jonte1346/Service-Robotics/CAD/Laser files/Front Panel 2.DXF

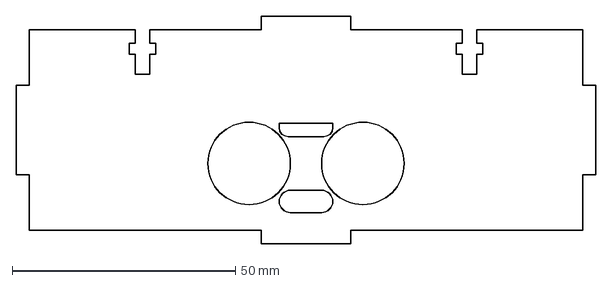
[picture p29: CAD file, 2024-11-29]
CAD/Laser files/Front Panel 2.DXF
130.0 x 51.0 mm
