jonte1346/Service-Robotics/CAD/Batterihållare/Bas.SLDPRT

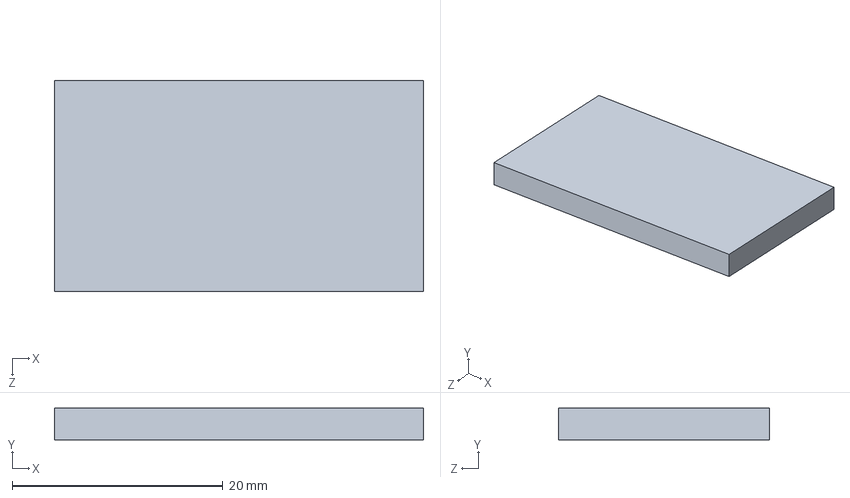
[picture p30: CAD file, 2024-12-06]
CAD/Batterihållare/Bas.SLDPRT
35.0 x 3.00 x 20.0 mm
