jonte1346/Service-Robotics/CAD/Body V5 (V2)/Side Panel 2.SLDPRT

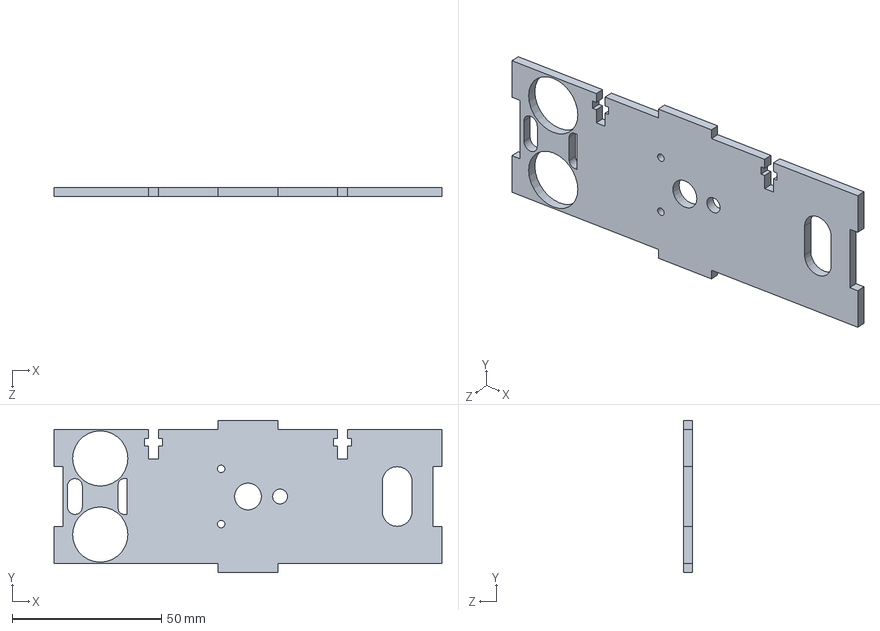
[picture p31: CAD file, 2024-11-29]
CAD/Body V5 (V2)/Side Panel 2.SLDPRT
130.0 x 51.0 x 3.00 mm
