jonte1346/Service-Robotics/CAD/Laser files/Cage Side.DXF

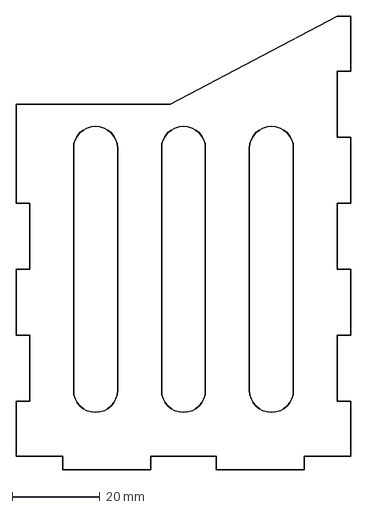
[picture p32: CAD file, 2024-11-29]
CAD/Laser files/Cage Side.DXF
76.0 x 103.0 mm
