jonte1346/Service-Robotics/CAD/Batterihållare/Front.SLDPRT

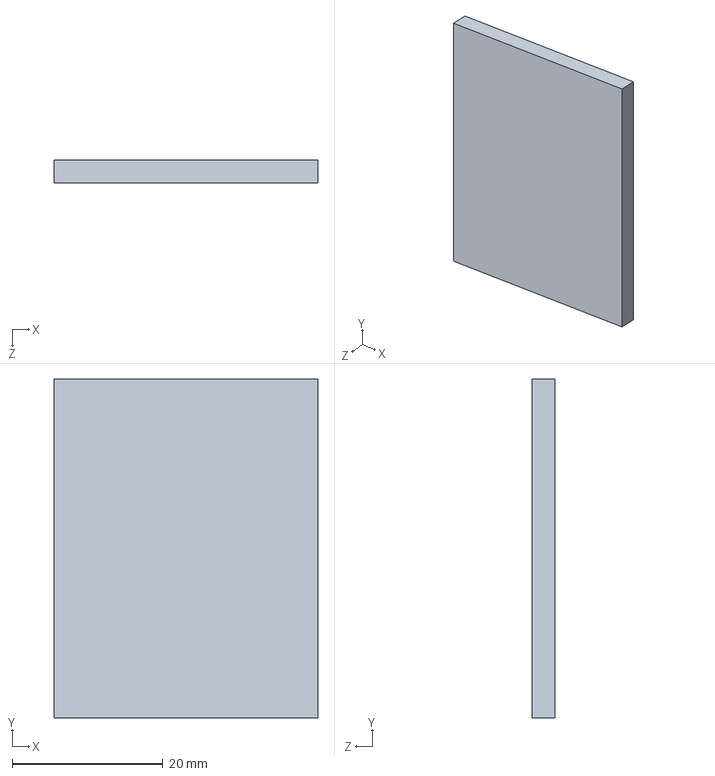
[picture p33: CAD file, 2024-12-06]
CAD/Batterihållare/Front.SLDPRT
35.0 x 45.0 x 3.00 mm
