jonte1346/Service-Robotics/CAD/Laser files/Side Panel 2.DXF

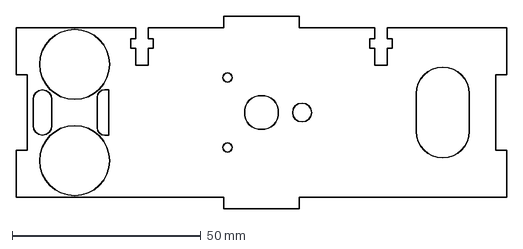
[picture p34: CAD file, 2024-11-29]
CAD/Laser files/Side Panel 2.DXF
130.0 x 51.0 mm
