jonte1346/Service-Robotics/CAD/Body V5 (V2)/Cage Side.SLDPRT

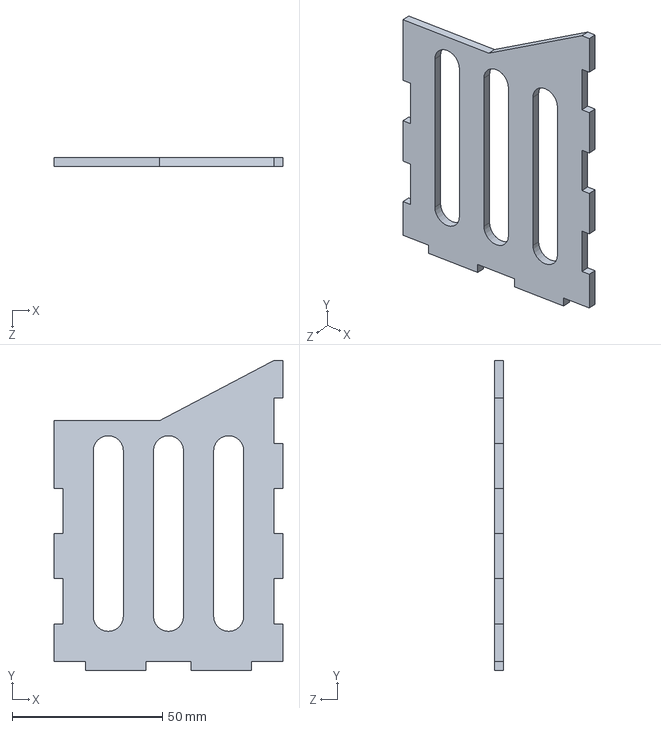
[picture p35: CAD file, 2024-11-29]
CAD/Body V5 (V2)/Cage Side.SLDPRT
76.0 x 103.0 x 3.00 mm
