jonte1346/Service-Robotics/CAD/Laser files/Cage Right.DXF

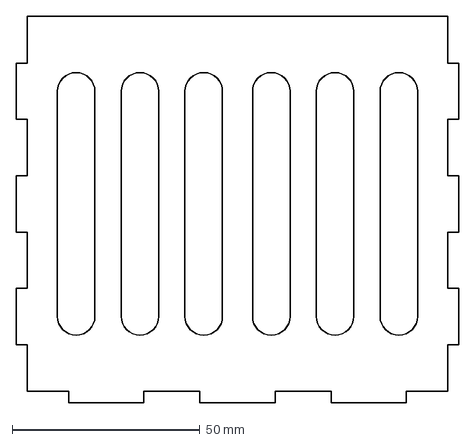
[picture p36: CAD file, 2024-11-29]
CAD/Laser files/Cage Right.DXF
118.0 x 103.0 mm
