jonte1346/Service-Robotics/CAD/Body V5 (V2)/Arm.SLDPRT

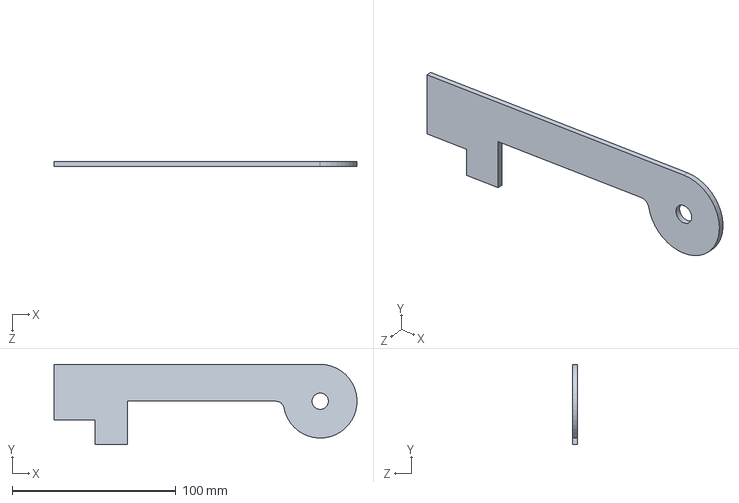
[picture p37: CAD file, 2024-11-29]
CAD/Body V5 (V2)/Arm.SLDPRT
185.0 x 49.0 x 3.00 mm
