jonte1346/Service-Robotics/CAD/Laser files/Top Panel 2.DXF

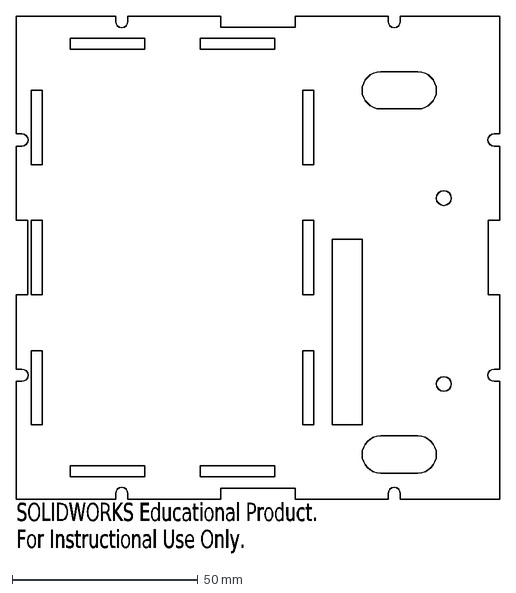
[picture p38: CAD file, 2024-11-29]
CAD/Laser files/Top Panel 2.DXF
SOLIDWORKS Educational Product.
For Instructional Use Only.
