jonte1346/Service-Robotics/CAD/Laser files/Arm - arm spacer.DXF

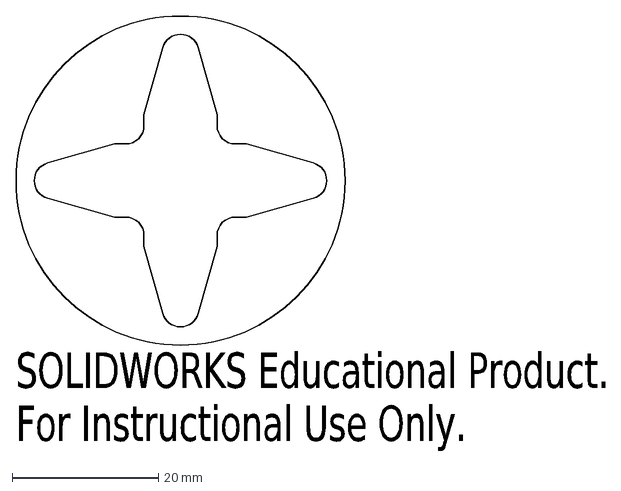
[picture p40: CAD file, 2024-11-29]
CAD/Laser files/Arm - arm spacer.DXF
SOLIDWORKS Educational Product.
For Instructional Use Only.
