jonte1346/Service-Robotics/CAD/Body V5 (V2)/Cage Left.SLDPRT

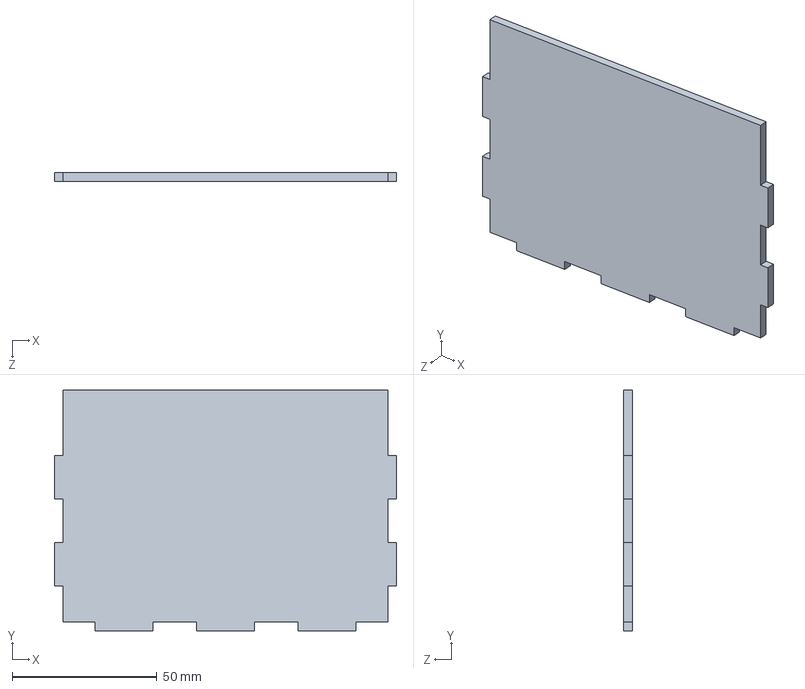
[picture p41: CAD file, 2024-11-29]
CAD/Body V5 (V2)/Cage Left.SLDPRT
118.0 x 83.0 x 3.00 mm
