jonte1346/Service-Robotics/CAD/Laser files/Cage Left.DXF

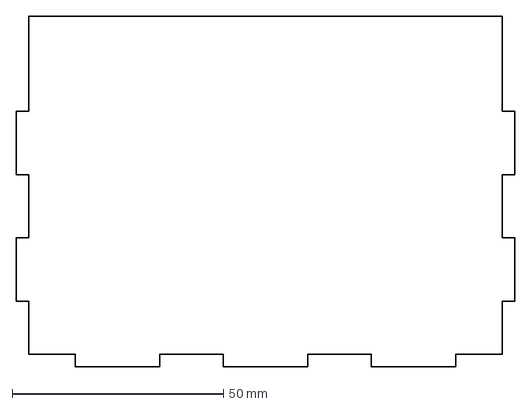
[picture p42: CAD file, 2024-11-29]
CAD/Laser files/Cage Left.DXF
118.0 x 83.0 mm
