jonte1346/Service-Robotics/CAD/Laser files/Arm - gripper support.DXF

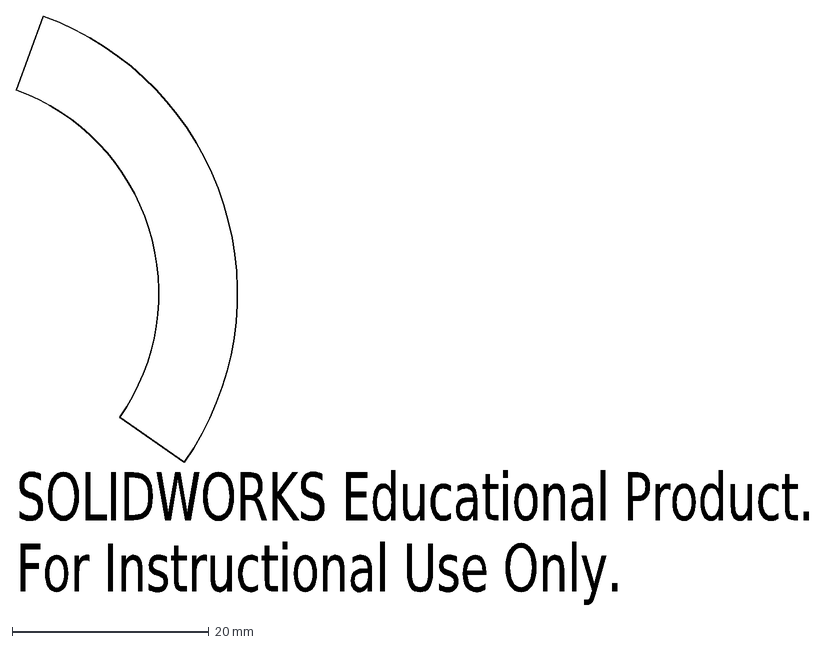
[picture p43: CAD file, 2024-11-29]
CAD/Laser files/Arm - gripper support.DXF
SOLIDWORKS Educational Product.
For Instructional Use Only.
