jonte1346/Service-Robotics/CAD/Body V5 (V2)/Top Panel 2.SLDPRT

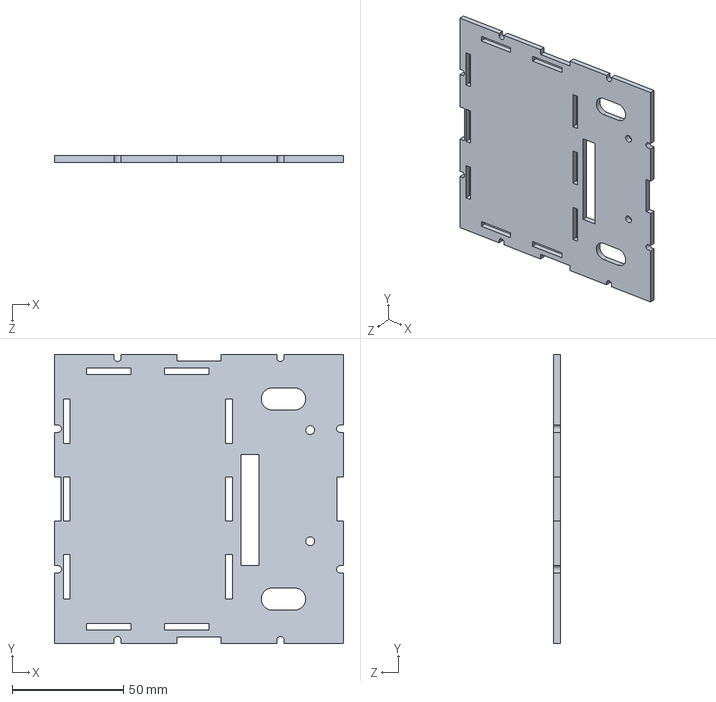
[picture p44: CAD file, 2024-11-28]
CAD/Body V5 (V2)/Top Panel 2.SLDPRT
130.0 x 130.0 x 3.00 mm
