jonte1346/Service-Robotics/CAD/Laser files/Arm - hålbricka.DXF

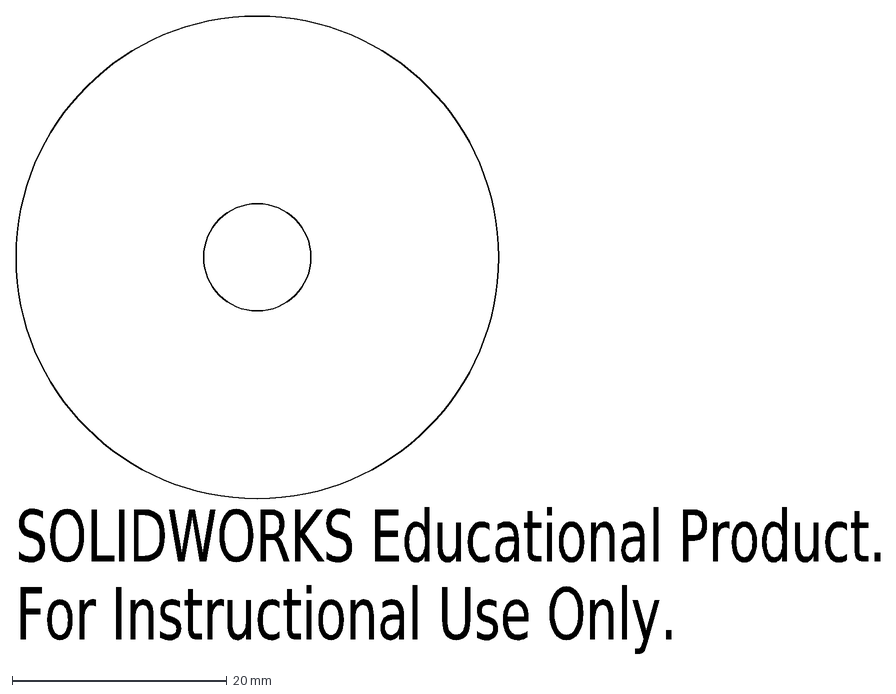
[picture p45: CAD file, 2024-11-29]
CAD/Laser files/Arm - hålbricka.DXF
SOLIDWORKS Educational Product.
For Instructional Use Only.
