jonte1346/Service-Robotics/CAD/Body V5 (V2)/Spacer.SLDPRT

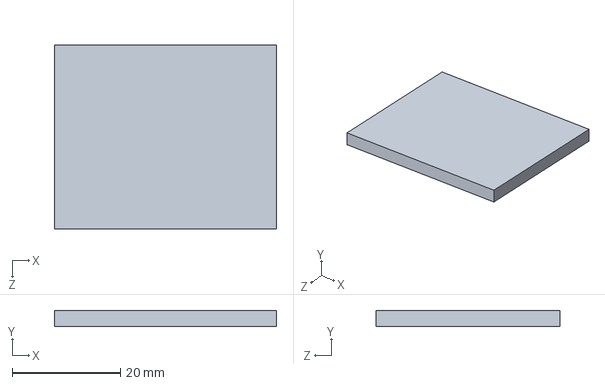
[picture p46: CAD file, 2024-11-27]
CAD/Body V5 (V2)/Spacer.SLDPRT
41.0 x 3.00 x 34.0 mm
