jonte1346/Service-Robotics/CAD/Laser files/Arm.DXF

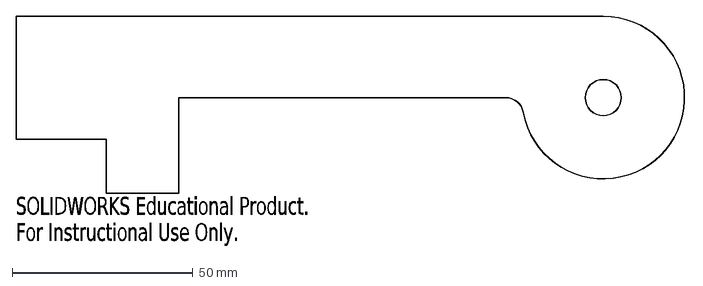
[picture p47: CAD file, 2024-11-29]
CAD/Laser files/Arm.DXF
SOLIDWORKS Educational Product.
For Instructional Use Only.
