jonte1346/Service-Robotics/CAD/Body V5 (V2)/Servo bult platta.SLDPRT

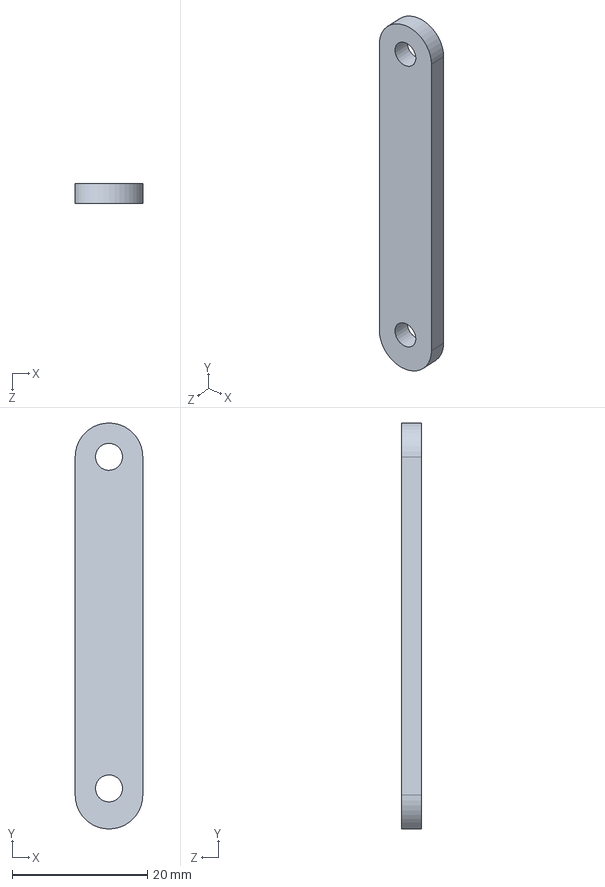
[picture p48: CAD file, 2024-11-25]
CAD/Body V5 (V2)/Servo bult platta.SLDPRT
10.0 x 60.0 x 3.00 mm
