jonte1346/Service-Robotics/CAD/Laser files/Servo Spacer.DXF

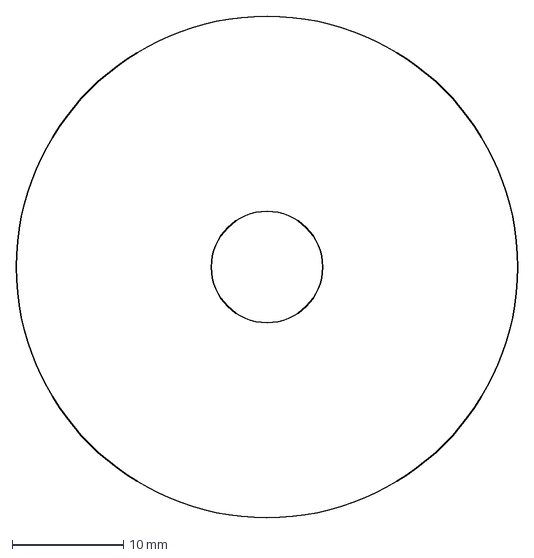
[picture p49: CAD file, 2024-11-20]
CAD/Laser files/Servo Spacer.DXF
45.0 x 45.0 mm
