jonte1346/Service-Robotics/CAD/Laser files/Servo bult platta.DXF

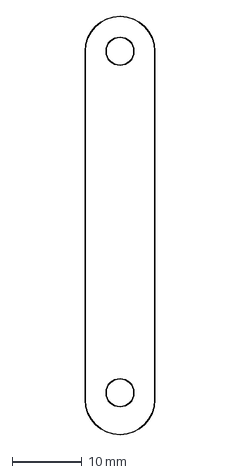
[picture p50: CAD file, 2024-11-20]
CAD/Laser files/Servo bult platta.DXF
10.0 x 60.0 mm
