jonte1346/Service-Robotics/CAD/Body V5 (V2)/Cage ramp.SLDPRT

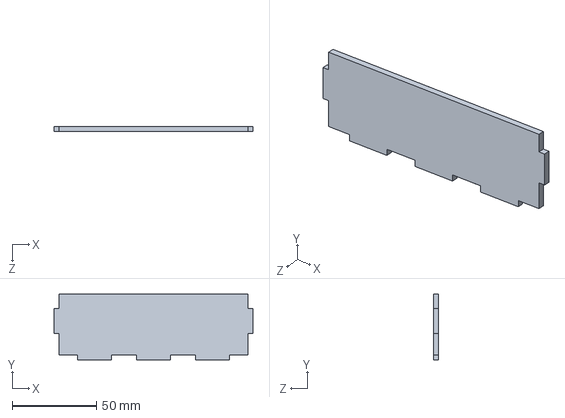
[picture p51: CAD file, 2024-11-20]
CAD/Body V5 (V2)/Cage ramp.SLDPRT
118.0 x 39.0 x 3.00 mm
