jonte1346/Service-Robotics/CAD/Laser files/Cage ramp.DXF

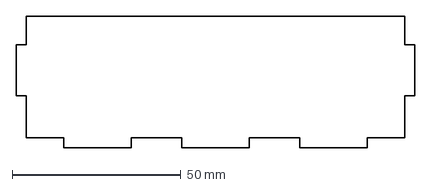
[picture p52: CAD file, 2024-11-20]
CAD/Laser files/Cage ramp.DXF
118.0 x 39.0 mm
