jonte1346/Service-Robotics/CAD/Body V5 (V2)/Cage ramp support.SLDPRT

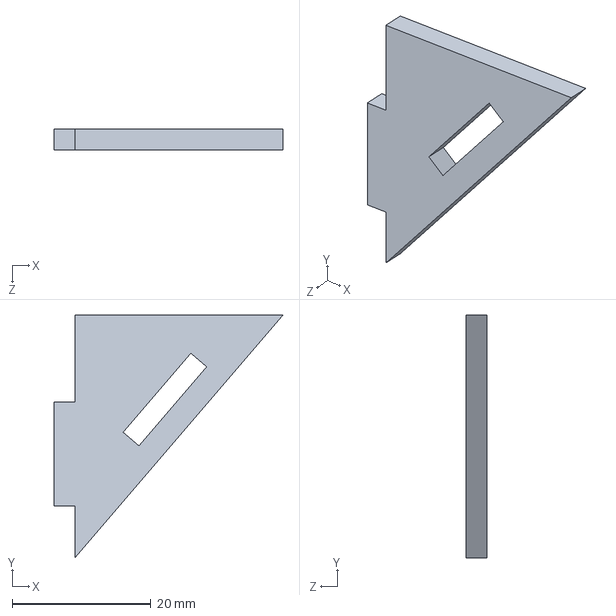
[picture p53: CAD file, 2024-11-20]
CAD/Body V5 (V2)/Cage ramp support.SLDPRT
33.0 x 35.0 x 3.00 mm
