jonte1346/Service-Robotics/CAD/Laser files/Cage ramp support.DXF

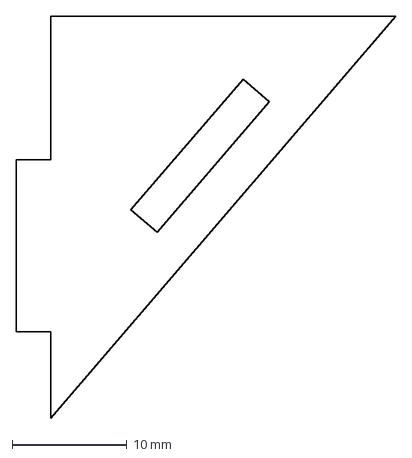
[picture p54: CAD file, 2024-11-20]
CAD/Laser files/Cage ramp support.DXF
33.0 x 35.0 mm
