jonte1346/Service-Robotics/CAD/Laser files/Back Panel 2.DXF

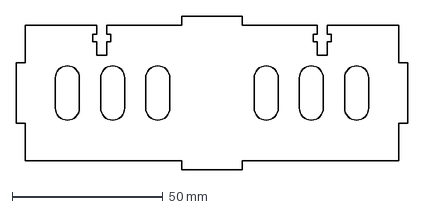
[picture p55: CAD file, 2024-11-20]
CAD/Laser files/Back Panel 2.DXF
130.0 x 51.0 mm
