jonte1346/Service-Robotics/CAD/Body V5 (V2)/Wooden cylinder.SLDPRT

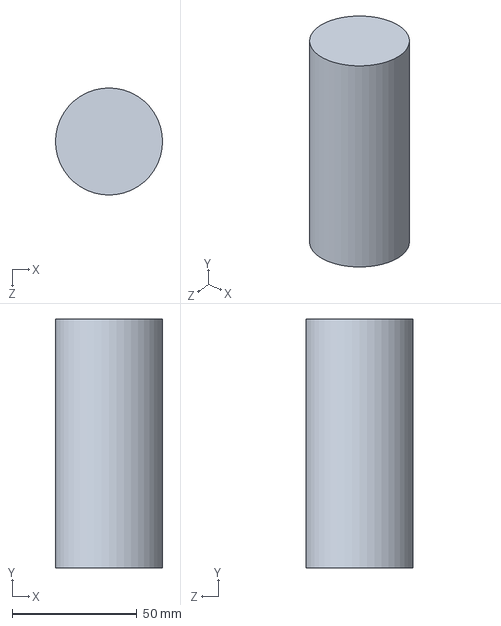
[picture p56: CAD file, 2024-11-18]
CAD/Body V5 (V2)/Wooden cylinder.SLDPRT
43.0 x 100.0 x 43.0 mm
