jonte1346/Service-Robotics/sketch0212/main/driving.ino

// Movement functions
void moveForward() {
  motorLeft.setSpeed(150);
  motorRight.setSpeed(150);
}

void turnLeft() {
  motorLeft.setSpeed(-100);
  motorRight.setSpeed(100);
  changeOrientation(true);
  delay(500);
}

void turnRight() {
  motorLeft.setSpeed(100);
  motorRight.setSpeed(-100);
  changeOrientation(false);
  delay(500);
}

void turnAround() {
  motorLeft.setSpeed(-150);
  motorRight.setSpeed(150);
  changeOrientation(true);
  changeOrientation(true);
  delay(1000);
}

void stopMotors() {
  motorLeft.setSpeed(0);
  motorRight.setSpeed(0);
}
